buentead/ADIRS/docu/images/stateAdir.png

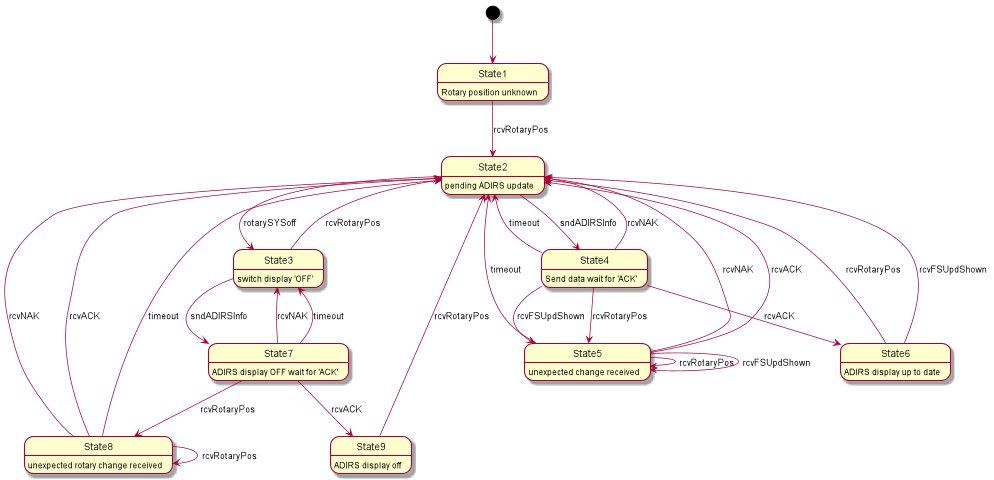
docu/images/stateAdir.png
