buentead/ADIRS/docu/images/stateBattery.png

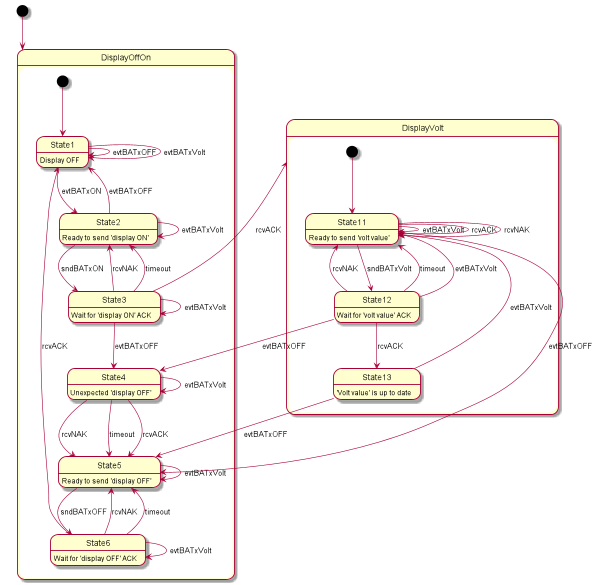
docu/images/stateBattery.png
