buentead/ADIRS/docu/images/stateIRx.png

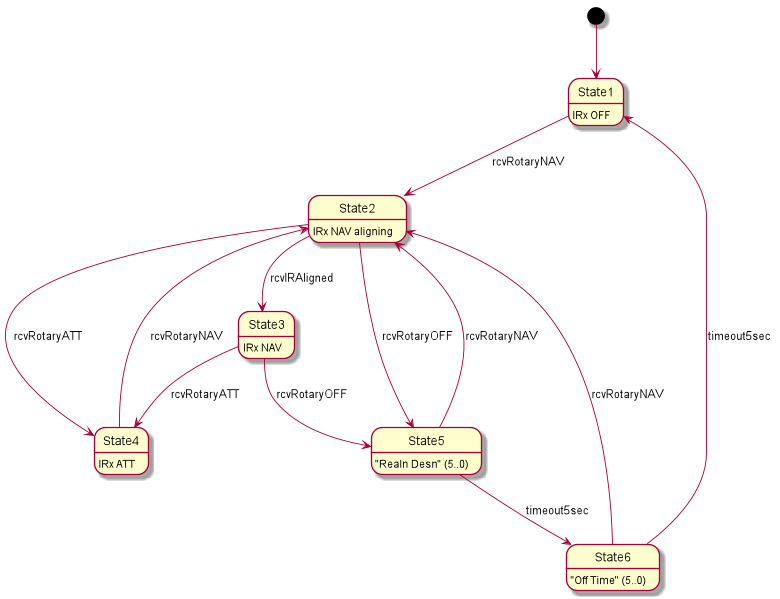
docu/images/stateIRx.png
