buentead/ADIRS/docu/images/StateTripleGauge.png

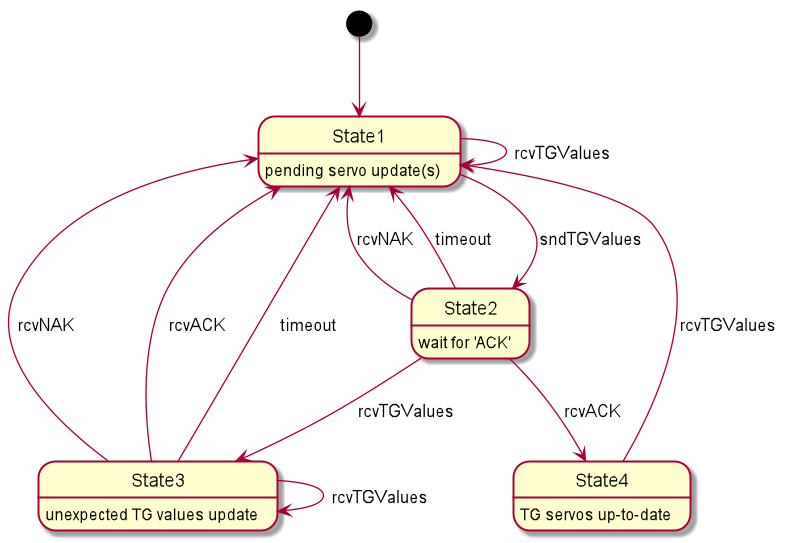
docu/images/StateTripleGauge.png
