buentead/ADIRS/hardware/adiru/ADIRU_bb.jpg

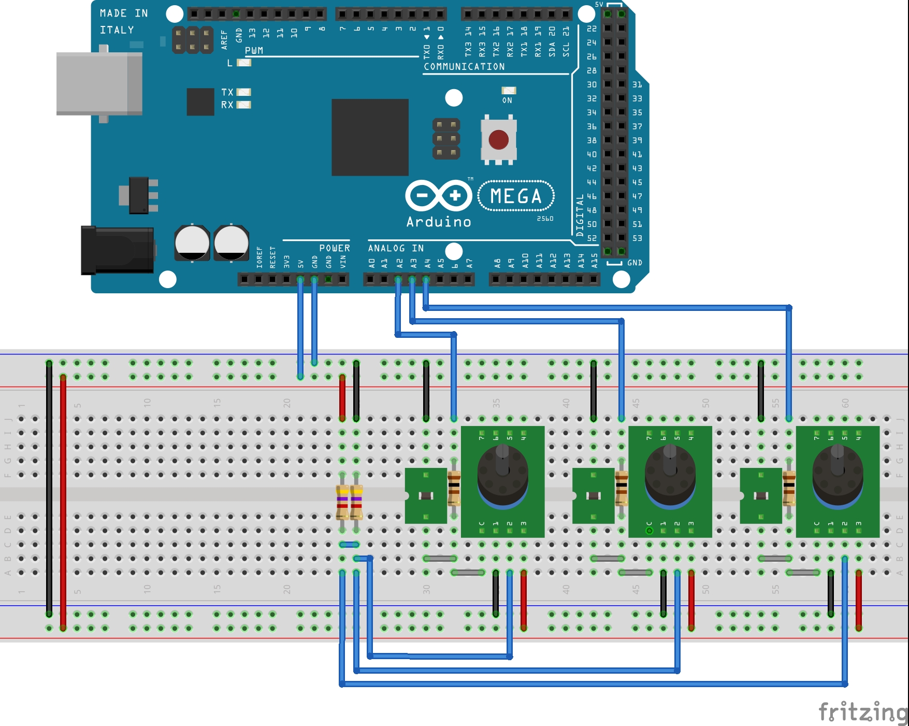
hardware/adiru/ADIRU_bb.jpg
