buentead/ADIRS/hardware/battery/BAT_bb.jpg

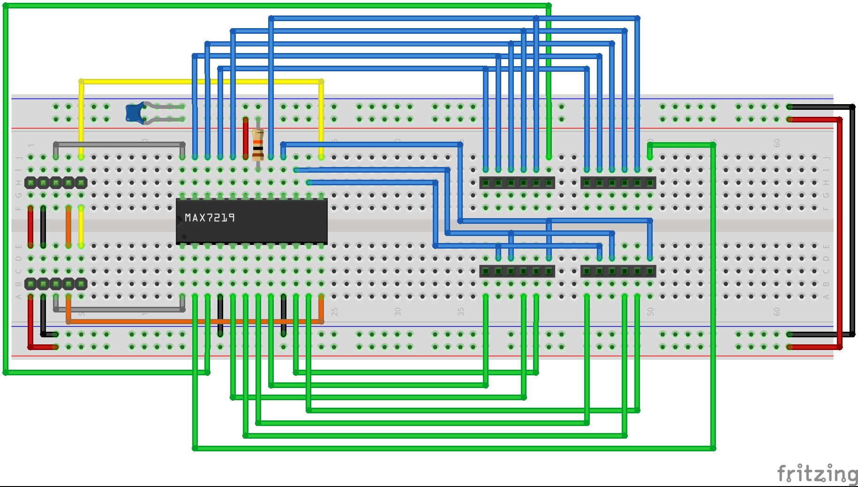
hardware/battery/BAT_bb.jpg
